ElectronicCats/Badge-BugCON2023/firmware/Badge/UartCommunication.cpp

#include "UartCommunication.h"

#if defined(ARCH_RP2040)
#include <EEPROM.h>
int addr = 0;
int talksCounterAddr = 2;
int receivedTalksOrderAddr = 4;
#endif

#ifdef ARDUINO_ARCH_MBED_RP2040
// 512KB block device, starting 1MB inside the flash
FlashIAPBlockDevice bd(XIP_BASE + 1024 * 1024, 1024 * 512);
mbed::TDBStore eeprom(&bd);
mbed::KVStore::info_t info;

#endif
uint8_t rebootCounterBuffer[4];
uint16_t rebootCounter = 0;

const char *validTalks[] = {
    /*------col0------+--------col1--------+--------col2--------+--------col3--------+--------col4--------+--------col5--------+--------col6--------+--------col7--------+*/
    "Cloud Security -  The Blue Team Way",  // 0
    /*------col0------+--------col1--------+--------col2--------+--------col3--------+--------col4--------+--------col5--------+--------col6--------+--------col7--------+*/
    "Hacking Azure",  // 1
    /*------col0------+--------col1--------+--------col2--------+--------col3--------+--------col4--------+--------col5--------+--------col6--------+--------col7--------+*/
    "DevSecOps",  // 2
    /*------col0------+--------col1--------+--------col2--------+--------col3--------+--------col4--------+--------col5--------+--------col6--------+--------col7--------+*/
    "101 con Frida,    para hacking mobile",  // 3
    /*------col0------+--------col1--------+--------col2--------+--------col3--------+--------col4--------+--------col5--------+--------col6--------+--------col7--------+*/
    "OSINT for         Offensive Security.  Top 10 herramientas  mas populares -      Evelyn Hernandez",  // 4
    /*------col0------+--------col1--------+--------col2--------+--------col3--------+--------col4--------+--------col5--------+--------col6--------+--------col7--------+*/
    "100               vulnerabilidades en  30 dias: Hackeando   la mayor compania de seguros del mundo -  Alan Levy / Damian",  // 5
    /*------col0------+--------col1--------+--------col2--------+--------col3--------+--------col4--------+--------col5--------+--------col6--------+--------col7--------+*/
    "Necesitas un      equipo de respuesta  ante ciberataques y  no sabes por donde   comenzar? - Marco    Mendoza / Gabriela",  // 6
    /*------col0------+--------col1--------+--------col2--------+--------col3--------+--------col4--------+--------col5--------+--------col6--------+--------col7--------+*/
    "Tales From a Cloud CSIRT- Lets deep    dive into a          Kubernetes (k8s)     Infection            - Santiago Abastante",  // 7
    /*------col0------+--------col1--------+--------col2--------+--------col3--------+--------col4--------+--------col5--------+--------col6--------+--------col7--------+*/
    "Como probar       nuestro plan de      respuesta a          incidentes de manera eficaz? - Julio Cesar Munoz Hernandez",  // 8
    /*------col0------+--------col1--------+--------col2--------+--------col3--------+--------col4--------+--------col5--------+--------col6--------+--------col7--------+*/
    "Brute Forcing and Destroy with IA      - Debug Sec",  // 9
    /*------col0------+--------col1--------+--------col2--------+--------col3--------+--------col4--------+--------col5--------+--------col6--------+--------col7--------+*/
    "Evolving the      Threat Landscape:    The Rise of     Post-exploitation         - Maria Isabel       Manjarrez",  // 10
    /*------col0------+--------col1--------+--------col2--------+--------col3--------+--------col4--------+--------col5--------+--------col6--------+--------col7--------+*/
    "Querida,          descentralice a los  ninos                - St4t3",  // 11
    /*------col0------+--------col1--------+--------col2--------+--------col3--------+--------col4--------+--------col5--------+--------col6--------+--------col7--------+*/
    "Revelando el      talon de Aquiles:    explorando trucos de ingenieria social    usando aplicaciones  con interaccion      humana directa       - Mauro Parra",  // 12
    /*------col0------+--------col1--------+--------col2--------+--------col3--------+--------col4--------+--------col5--------+--------col6--------+--------col7--------+*/
    "El Lado Oscuro de la Concientizacion:  Como el Phishing     Interno Puede Salvar a tu Empresa - Jesus Barajas",  // 13
    /*------col0------+--------col1--------+--------col2--------+--------col3--------+--------col4--------+--------col5--------+--------col6--------+--------col7--------+*/
    "Rate limit es     importante? -  Felix Morales",  // 14
    /*------col0------+--------col1--------+--------col2--------+--------col3--------+--------col4--------+--------col5--------+--------col6--------+--------col7--------+*/
    "Hacking Azure -   Joaquin Molina",  // 15
    /*------col0------+--------col1--------+--------col2--------+--------col3--------+--------col4--------+--------col5--------+--------col6--------+--------col7--------+*/
    "Como meterse a la fila de forma        elegante - Virgilio  Castro",  // 16
    /*------col0------+--------col1--------+--------col2--------+--------col3--------+--------col4--------+--------col5--------+--------col6--------+--------col7--------+*/
    "NLPs y NERs:      Hablando y           compartiendo datos en modelos de Machine  Learning en un       lenguaje seguro -    Salvador Mendoza",  // 17
    /*------col0------+--------col1--------+--------col2--------+--------col3--------+--------col4--------+--------col5--------+--------col6--------+--------col7--------+*/
    "Bug bounty 101    - Adrian Pedrazzoli",  // 18
    /*------col0------+--------col1--------+--------col2--------+--------col3--------+--------col4--------+--------col5--------+--------col6--------+--------col7--------+*/
    "Security or       Espionage - Dhave    Security",  // 19
    /*------col0------+--------col1--------+--------col2--------+--------col3--------+--------col4--------+--------col5--------+--------col6--------+--------col7--------+*/
    "Advanced          Persistent Threat -  1: Como              desestabilizar un    pais - Jonathan      Palacios",  // 20
    /*------col0------+--------col1--------+--------col2--------+--------col3--------+--------col4--------+--------col5--------+--------col6--------+--------col7--------+*/
    "Definiendo        requisitos de        seguridad sin morir  en el intento        - Arturo Sustaita",  // 21
    /*------col0------+--------col1--------+--------col2--------+--------col3--------+--------col4--------+--------col5--------+--------col6--------+--------col7--------+*/
    "Mi camino a los   2500 puntos de       reputacion en        Hackerone            - Adrian Pedrazzoli",  // 22
    /*------col0------+--------col1--------+--------col2--------+--------col3--------+--------col4--------+--------col5--------+--------col6--------+--------col7--------+*/
    "pulsioximetro IoT usando Arduino y     Node MCU             - Wulfrano Moreno",  // 23
    /*------col0------+--------col1--------+--------col2--------+--------col3--------+--------col4--------+--------col5--------+--------col6--------+--------col7--------+*/
    "De BugCON a       Almoloya: full       disclosure           - Luis Velazquez",  // 24
    /*------col0------+--------col1--------+--------col2--------+--------col3--------+--------col4--------+--------col5--------+--------col6--------+--------col7--------+*/
    "Me fui por bug    bounty mobile y esto me paso              - Jacobo Tibaquira",  // 25
    /*------col0------+--------col1--------+--------col2--------+--------col3--------+--------col4--------+--------col5--------+--------col6--------+--------col7--------+*/
    "Porque todos      vulneran pero nadie  hace contencion y    mitigacion           - Irving Paz",  // 26
    /*------col0------+--------col1--------+--------col2--------+--------col3--------+--------col4--------+--------col5--------+--------col6--------+--------col7--------+*/
    "Hacking etico     potenciado por       inteligencia         artificial: El       matrimonio perfecto  - Raul Aguilera      Andrade / Luis Daniel Aguirre Cueva",  // 27
    /*------col0------+--------col1--------+--------col2--------+--------col3--------+--------col4--------+--------col5--------+--------col6--------+--------col7--------+*/
    "Como hacer        ciberseguridad       Aplicando            Inteligencia         Artificial           - Pablo Corona"};  // 28

UartCommunication::UartCommunication() {
  this->communication = false;
  this->receivedSuccess = false;
  this->talksCounter = 0;
  this->ssid = "Badge " + getID();
  this->password = "password";
}

void UartCommunication::begin() {
#ifdef ARDUINO_ARCH_MBED_RP2040
  eeprom.init();

  if (eeprom.get_info("rebootCounter", &info) != MBED_ERROR_ITEM_NOT_FOUND) {
    debug.println("Key size: " + String(info.size));
    eeprom.get("rebootCounter", rebootCounterBuffer, info.size);
    rebootCounter = *((uint16_t *)rebootCounterBuffer);
    debug.println("Reboot counter: " + String(rebootCounter));
    rebootCounter++;
    eeprom.set("rebootCounter", &rebootCounter, sizeof(rebootCounter), 0);
  } else {
    debug.println("Setting reboot counter");
    eeprom.set("rebootCounter", &rebootCounter, sizeof(rebootCounter), 0);
  }

  if (eeprom.get_info("talksCounter", &info) != MBED_ERROR_ITEM_NOT_FOUND) {
    debug.println("Key size: " + String(info.size));
    eeprom.get("talksCounter", talksCounterBuffer, info.size);
    talksCounter = *((uint8_t *)talksCounterBuffer);
    debug.println("Talks counter: " + String(talksCounter));
  } else {
    debug.println("Setting talks counter");
    eeprom.set("talksCounter", &talksCounter, sizeof(talksCounter), 0);
  }

  if (eeprom.get_info("receivedTalksOrder", &info) != MBED_ERROR_ITEM_NOT_FOUND) {
    debug.println("Key size: " + String(info.size));
    eeprom.get("receivedTalksOrder", receivedTalksOrderBuffer, info.size);
    memcpy(receivedTalksOrder, receivedTalksOrderBuffer, sizeof(receivedTalksOrder));
    debug.println("Received talks order: ");
    for (size_t i = 0; i < sizeof(receivedTalksOrder) / sizeof(receivedTalksOrder[0]); i++) {
      debug.println(String(i) + ": " + String(receivedTalksOrder[i]));
    }
  } else {
    debug.println("Setting received talks order");
    eeprom.set("receivedTalksOrder", receivedTalksOrder, sizeof(receivedTalksOrder), 0);
  }

  // Fill talk list
  for (size_t i = 0; i < talksCounter; i++) {
    talkList.push_back(String(validTalks[receivedTalksOrder[i]]));
    debug.println("Talk " + String(i) + ": " + talkList[i]);
  }
#endif
#ifdef ARCH_RP2040
  EEPROM.begin(512);
  rebootCounter = EEPROM.read(addr);
  debug.println("Reboot counter: " + String(rebootCounter));
  rebootCounter++;
  EEPROM.write(addr, rebootCounter);
  EEPROM.commit();

  talksCounter = EEPROM.read(talksCounterAddr);
  talksCounter = talksCounter == 255 ? 0 : talksCounter;
  debug.println("Talks counter: " + String(talksCounter));

  for (size_t i = 0; i < sizeof(receivedTalksOrder) / sizeof(receivedTalksOrder[0]); i++) {
    // receivedTalksOrder[i] = EEPROM.read(receivedTalksOrderAddr + i);
    int value = EEPROM.read(receivedTalksOrderAddr + i);
    if (value == 255) {
      receivedTalksOrder[i] = 0;
    } else {
      receivedTalksOrder[i] = value;
    }
    debug.println(String(i) + ": " + String(receivedTalksOrder[i]));
  }

  // Fill talk list
  for (size_t i = 0; i < talksCounter; i++) {
    talkList.push_back(String(validTalks[receivedTalksOrder[i]]));
    debug.println("Talk " + String(i) + ": " + talkList[i]);
  }
#endif
}

void UartCommunication::ereaseFlash() {
#ifdef ARDUINO_ARCH_MBED_RP2040
  talksCounter = 0;
  eeprom.set("talksCounter", &talksCounter, sizeof(talksCounter), 0);
  memset(receivedTalksOrder, 0, sizeof(receivedTalksOrder));
  eeprom.set("receivedTalksOrder", receivedTalksOrder, sizeof(receivedTalksOrder), 0);
#endif
#ifdef ARCH_RP2040
  talksCounter = 0;
  EEPROM.write(talksCounterAddr, talksCounter);
  EEPROM.commit();
  for (size_t i = 0; i < sizeof(receivedTalksOrder) / sizeof(receivedTalksOrder[0]); i++) {
    EEPROM.write(receivedTalksOrderAddr + i, 0);
    EEPROM.commit();
  }
#endif
}

void UartCommunication::updateTalkList(String talkName) {
  talkName.trim();
  // Check if talkName is valid
  bool isValid = false;
  size_t index;
  for (index = 0; index < sizeof(validTalks) / sizeof(validTalks[0]); index++) {
    if (strcmp(validTalks[index], talkName.c_str()) == 0) {
      debug.println("'" + String(validTalks[index]) + "' == '" + talkName + "'");
      isValid = true;
      break;
    }
  }

  if (!isValid) {
    // debug.println("Invalid talk name: '" + talkName + "'");
    return;
  }

  debug.println("Updating talk list");

  // Check if talkName is already in the list
  for (size_t i = 0; i < talkList.size(); i++) {
    if (talkList[i] == talkName) {
      debug.println("Talk already in list");
      return;
    }
  }

  talkList.push_back(talkName);
  // debug.println("Talk list size: " + String(talkList.size()));
  for (size_t i = 0; i < talkList.size(); i++) {
    debug.println("Talk " + String(i) + ": " + talkList[i]);
  }

  this->receivedSuccess = true;

  // Update talks order with index
  debug.println("New talk index: " + String(index));
  receivedTalksOrder[talksCounter] = index;
#ifdef ARDUINO_ARCH_MBED_RP2040
  eeprom.set("receivedTalksOrder", receivedTalksOrder, sizeof(receivedTalksOrder), 0);
#endif
#ifdef ARCH_RP2040
  EEPROM.write(receivedTalksOrderAddr + talksCounter, index);
  EEPROM.commit();
#endif

  // Update talks counter
  talksCounter++;
#ifdef ARDUINO_ARCH_MBED_RP2040
  eeprom.set("talksCounter", &talksCounter, sizeof(talksCounter), 0);
#endif
#ifdef ARCH_RP2040
  EEPROM.write(talksCounterAddr, talksCounter);
  EEPROM.commit();
#endif
}

void UartCommunication::setTalk(uint8_t index) {
  this->talkName = String(validTalks[index]);
  debug.println("Setting talk: " + this->talkName);
}

String UartCommunication::getID() {
  String ID = "";
  char buff[4];
  for (size_t i = 0; i < 8; i++) {
    sprintf(buff, "%02X", (uint8_t)UniqueID8[i]);
    ID += buff;
  }
  return ID;
}

void UartCommunication::sendTalkName() {
#if defined(ESP32)
  static unsigned long lastTime = millis();

  if (millis() - lastTime > 1000) {
    Serial2.println(this->talkName);
    lastTime = millis();
  }
#endif
}

void UartCommunication::receiveTalkName() {
#ifdef RP2040
  if (Serial2.available()) {
    String input = Serial2.readStringUntil('\n');

    if (input.length() == 0) {
      debug.println("Empty input");
      return;
    }

    // debug.println("Received: " + input);

    // TODO: validate with a list of valid talk names
    updateTalkList(input);
  }
#endif
}

void UartCommunication::enableCommunication() {
  this->communication = true;
}

void UartCommunication::disableCommunication() {
  this->communication = false;
}

bool UartCommunication::isCommunicationEnabled() {
  return this->communication;
}

std::vector<String> UartCommunication::getTalkList() {
  return this->talkList;
}

String UartCommunication::getSSID() {
  return this->ssid;
}

String UartCommunication::getPassword() {
  return this->password;
}

String UartCommunication::getIP() {
  return this->ip;
}

void UartCommunication::setIP(String ip) {
  this->ip = ip;
}
