ElectronicCats/Badge-BugCON2023/firmware/Badge/styles.css.h

const char* styles_css = R"=====(body {
    font-family: Arial, sans-serif;
    display: flex;
    align-items: center;
    justify-content: center;
    height: 100vh;
    margin: 0;
}

.container {
    text-align: center;
}

label {
    display: block;
    margin-bottom: 5px;
}

input[type="range"] {
    width: 80%;
    padding: 5px;
    margin-bottom: 10px;
}

button {
    padding: 10px;
    background-color: #4CAF50;
    color: white;
    border: none;
    border-radius: 5px;
    cursor: pointer;
}

button:hover {
    background-color: #45a049;
}
)=====";
